cwbierwirth12/ESP32-home-temperature-sensors/hardware/Photos/espthsc/ESPTHSC-3.jpg

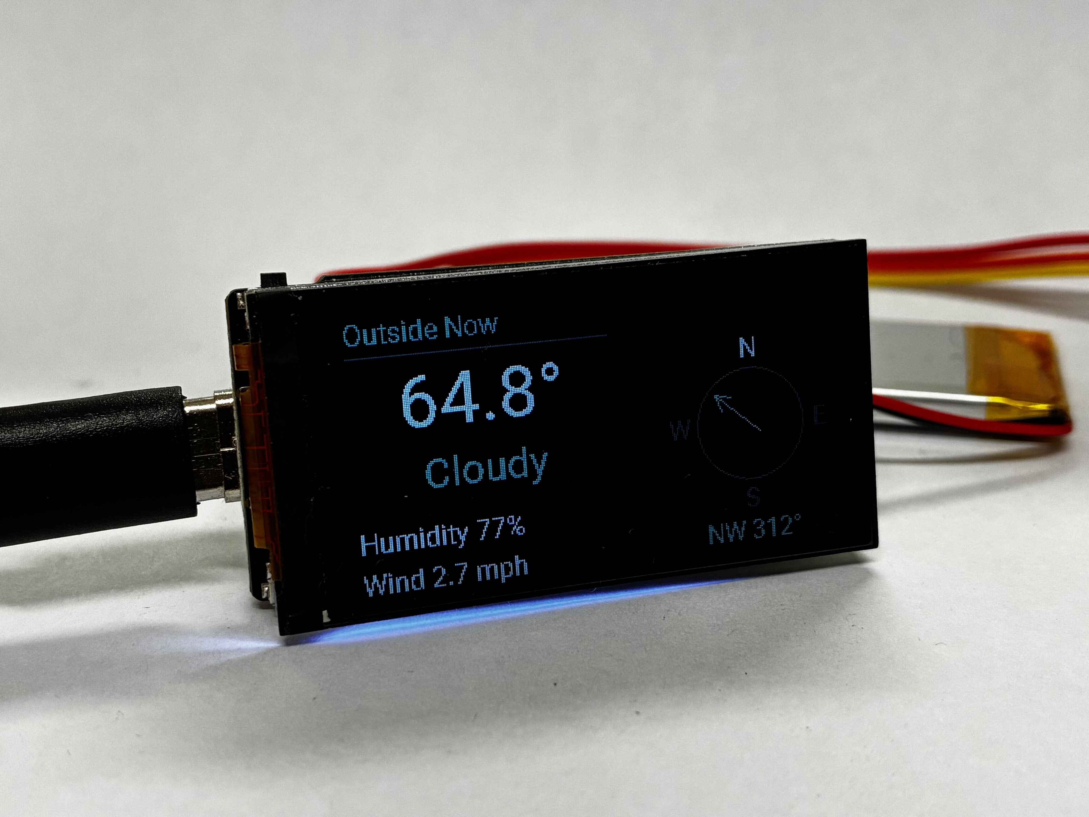
hardware/Photos/espthsc/ESPTHSC-3.jpg
