cwbierwirth12/ESP32-home-temperature-sensors/hardware/Photos/espth/espth-internal-assembly.jpg

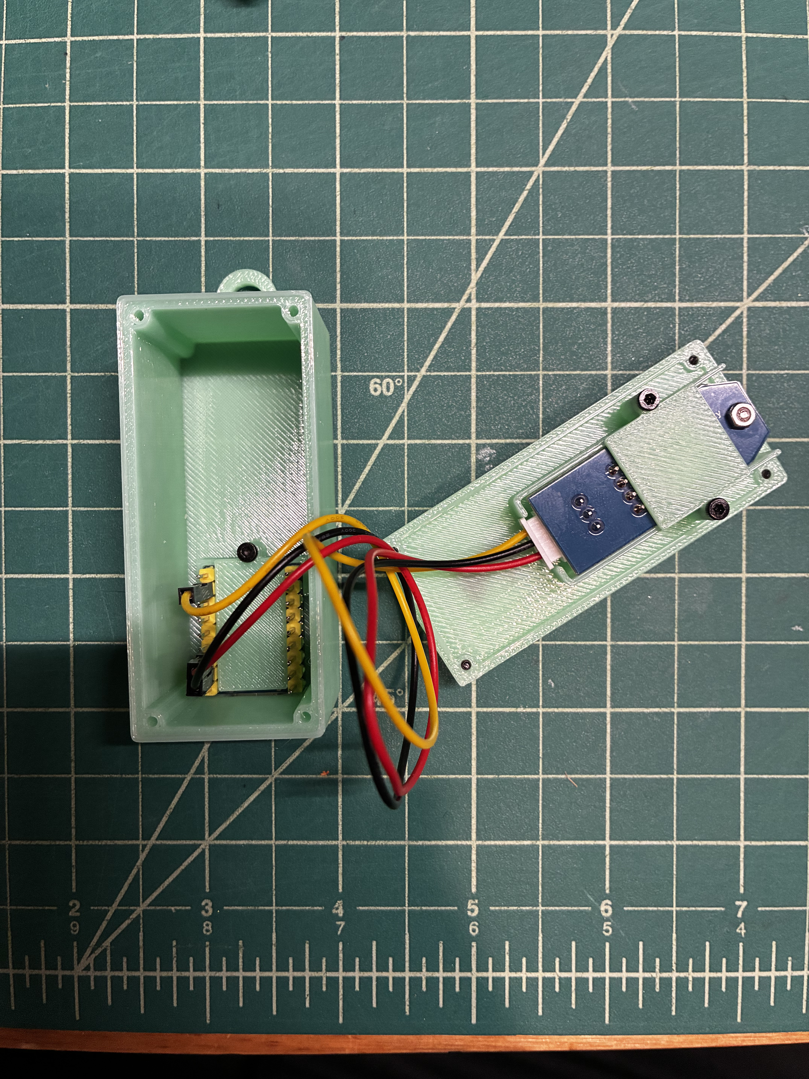
hardware/Photos/espth/espth-internal-assembly.jpg
